Axel051171/UniversalFluxInterface/firmware/include/ffconf.h

/**
 * FatFs R0.12c configuration (STM32CubeH7 Middlewares/Third_Party/FatFs) for the
 * soldered SD NAND: one volume, 8.3 names, FAT32, no RTC, no OS.
 */
#ifndef _FFCONF
#define _FFCONF 68300           /* revision ID, must match ff.h */

#define _FS_READONLY    0
#define _FS_MINIMIZE    0
#define _USE_STRFUNC    0
#define _USE_FIND       0
#define _USE_MKFS       1       /* blank chip: formatted on the first mount */
#define _USE_FASTSEEK   0
#define _USE_EXPAND     0
#define _USE_CHMOD      0
#define _USE_LABEL      1       /* volume label "UFI" */
#define _USE_FORWARD    0

#define _CODE_PAGE      437
#define _USE_LFN        0       /* DUMP0001.SCP */
#define _MAX_LFN        255
#define _LFN_UNICODE    0
#define _STRF_ENCODE    0
#define _FS_RPATH       0

#define _VOLUMES        1
#define _STR_VOLUME_ID  0
#define _VOLUME_STRS    "SD"
#define _MULTI_PARTITION 0
#define _MIN_SS         512
#define _MAX_SS         512
#define _USE_TRIM       0
#define _FS_NOFSINFO    0

#define _FS_TINY        0
#define _FS_EXFAT       0
#define _FS_NORTC       1       /* no RTC: every file gets this date */
#define _NORTC_MON      1
#define _NORTC_MDAY     1
#define _NORTC_YEAR     2026
#define _FS_LOCK        0
#define _FS_REENTRANT   0
#define _FS_TIMEOUT     1000
#define _SYNC_t         void*

#endif /* _FFCONF */
