Axel051171/UniversalFluxInterface/kicad/UFI_Headless/scripts/kisch.py

"""Minimal KiCad schematic writer.

Embeds symbols from the installed KiCad standard libraries (flattening derived
symbols), places instances and connects every pin through a short wire stub to
a power symbol, local label, global label or no-connect flag.  Electrical
connectivity is therefore fully defined by net names; the drawing is a clean
starting point that can be tidied up manually in Eeschema.
"""
from __future__ import annotations

import copy
import os
import re
import uuid as _uuid
from pathlib import Path

KICAD_SYM_DIR = Path(os.environ.get(
    "KICAD_SYMBOL_DIR", "C:/Program Files/KiCad/10.0/share/kicad/symbols"))
PROJECT_SYM_DIR = Path(__file__).resolve().parent.parent / "lib"
FORMAT_VERSION = "20231120"
STUB = 2.54
# Nets that are rendered as power symbols from the 'power' library
POWER_NETS = {"GND", "+3V3", "+5V", "+12V", "VBUS"}


class Q(str):
    """Quoted string atom (raw content, escapes preserved)."""


_TOKEN = re.compile(r'\(|\)|"(?:[^"\\]|\\.)*"|[^\s()]+')


def parse(text: str):
    stack: list[list] = [[]]
    for tok in _TOKEN.findall(text):
        if tok == "(":
            stack.append([])
        elif tok == ")":
            done = stack.pop()
            stack[-1].append(done)
        elif tok.startswith('"'):
            stack[-1].append(Q(tok[1:-1]))
        else:
            stack[-1].append(tok)
    return stack[0][0]


def dump(node, indent: int = 0) -> str:
    if isinstance(node, Q):
        return f'"{node}"'
    if not isinstance(node, list):
        return str(node)
    if all(not isinstance(c, list) for c in node):
        return "(" + " ".join(dump(c) for c in node) + ")"
    pad = "\t" * (indent + 1)
    head = [dump(c) for c in node if not isinstance(c, list)]
    out = "(" + " ".join(head)
    for c in node:
        if isinstance(c, list):
            out += "\n" + pad + dump(c, indent + 1)
    return out + "\n" + "\t" * indent + ")"


def child(node, key):
    for c in node:
        if isinstance(c, list) and c and c[0] == key:
            return c
    return None


_LIB_CACHE: dict[str, list] = {}


def _lib(lib: str):
    if lib not in _LIB_CACHE:
        # project-local library (kicad/UFI_Headless/lib) first, then the KiCad standard libraries
        local = PROJECT_SYM_DIR / f"{lib}.kicad_sym"
        path = local if local.exists() else KICAD_SYM_DIR / f"{lib}.kicad_sym"
        _LIB_CACHE[lib] = parse(path.read_text(encoding="utf8"))
    return _LIB_CACHE[lib]


def lib_symbol(lib: str, name: str):
    """Return a flattened copy of library symbol `name` (derived symbols resolved)."""
    for s in _lib(lib):
        if isinstance(s, list) and s[0] == "symbol" and s[1] == name:
            break
    else:
        raise KeyError(f"{lib}:{name} not found")
    ext = child(s, "extends")
    if not ext:
        return copy.deepcopy(s)
    base = lib_symbol(lib, ext[1])
    props = [c for c in s if isinstance(c, list) and c[0] == "property"]
    # 'ki_locked' is a symbol attribute that derived symbols inherit from the base
    props += [c for c in base if isinstance(c, list) and c[0] == "property" and c[1] == "ki_locked"]
    body = [c for c in base[2:] if not (isinstance(c, list) and c[0] in ("property", "extends"))]
    for c in body:
        if isinstance(c, list) and c[0] == "symbol":
            c[1] = Q(str(c[1]).replace(str(ext[1]), name, 1))
    first_sub = next(i for i, c in enumerate(body) if isinstance(c, list) and c[0] == "symbol")
    return ["symbol", Q(name)] + body[:first_sub] + props + body[first_sub:]
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
